Sarkis-S/Embedded_Workstation/media/workstation_rev_a/workstation_side.jpg

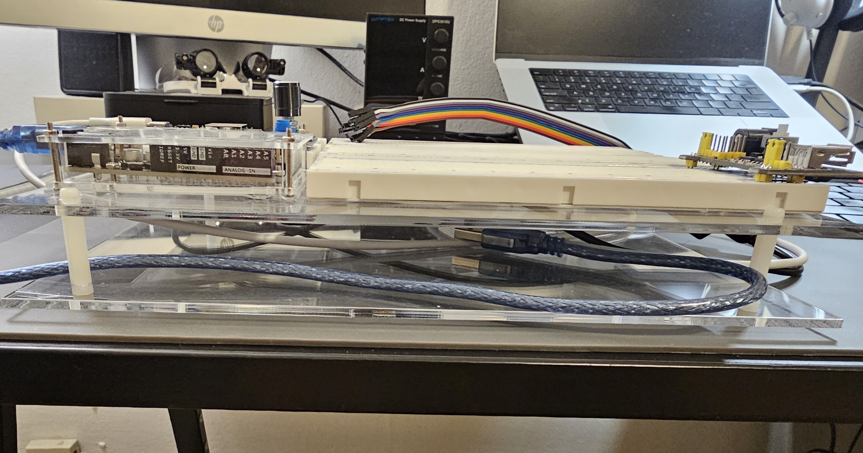
media/workstation_rev_a/workstation_side.jpg
