Sarkis-S/Embedded_Workstation/media/workbench_power_interface/perfboard_component_placing.png

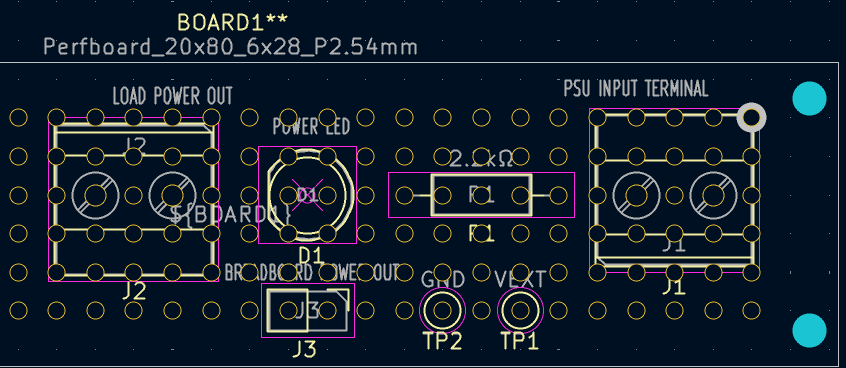
media/workbench_power_interface/perfboard_component_placing.png
