Sarkis-S/Embedded_Workstation/media/workbench_power_interface/perfboard_realistic_wiring.png

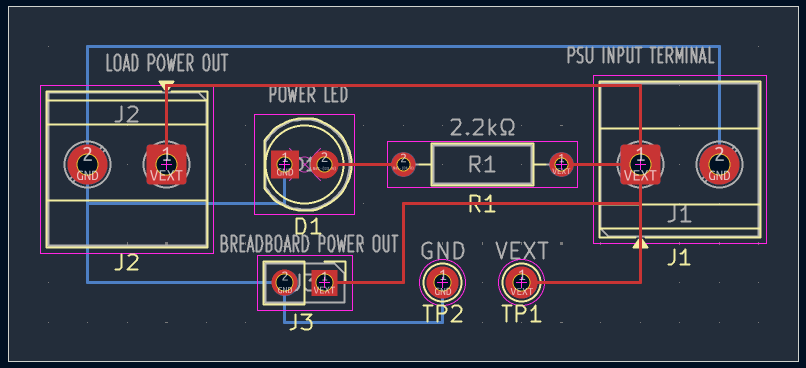
media/workbench_power_interface/perfboard_realistic_wiring.png
